potpurri/LiPo_Charger_TP4056_BuckBoost_TPS63020/imgs/3d-back-v1.1.png

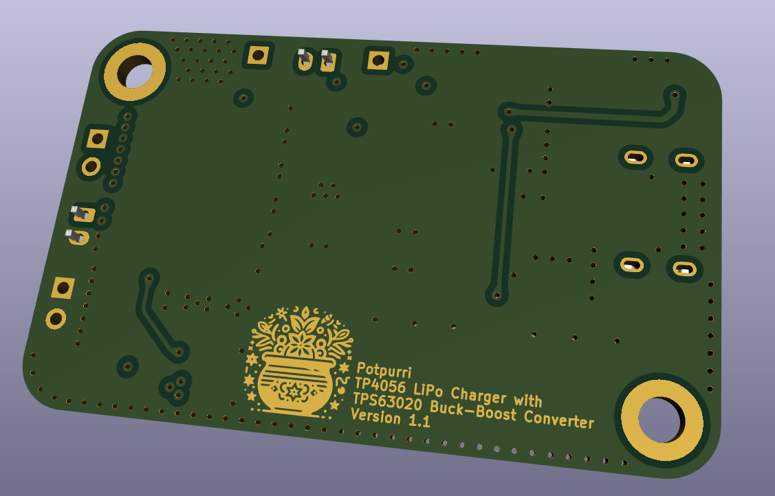
imgs/3d-back-v1.1.png
