potpurri/LiPo_Charger_TP4056_BuckBoost_TPS63020/imgs/3d-front-empty.png

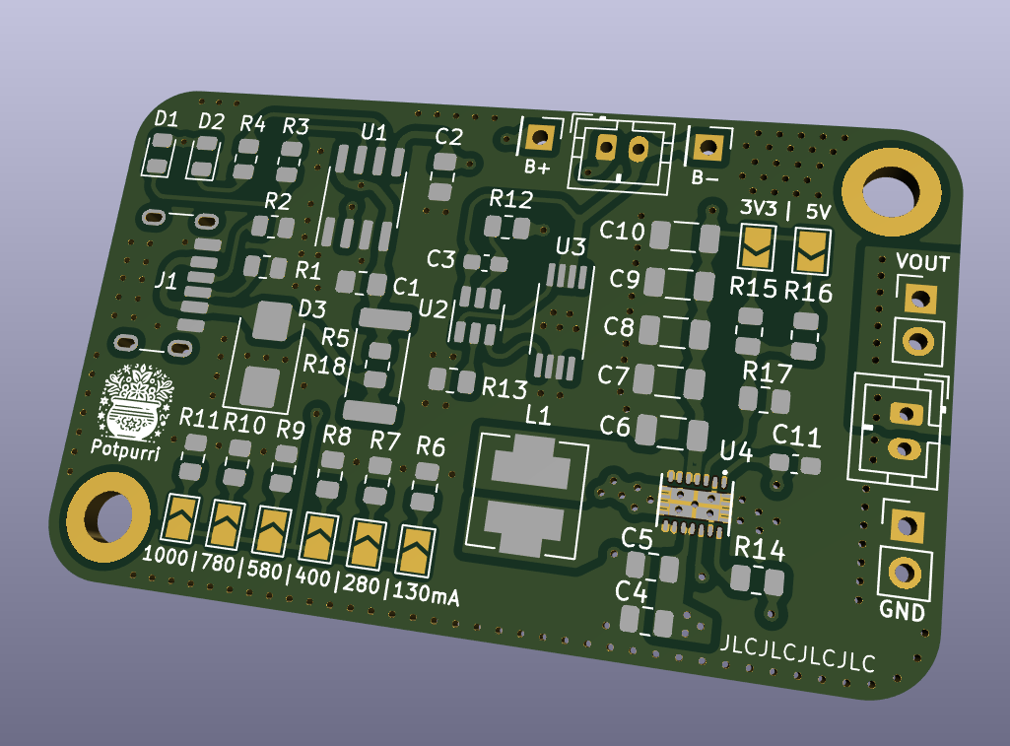
imgs/3d-front-empty.png
