potpurri/LiPo_Charger_TP4056_BuckBoost_TPS63020/imgs/pcb-back_v1.1.png

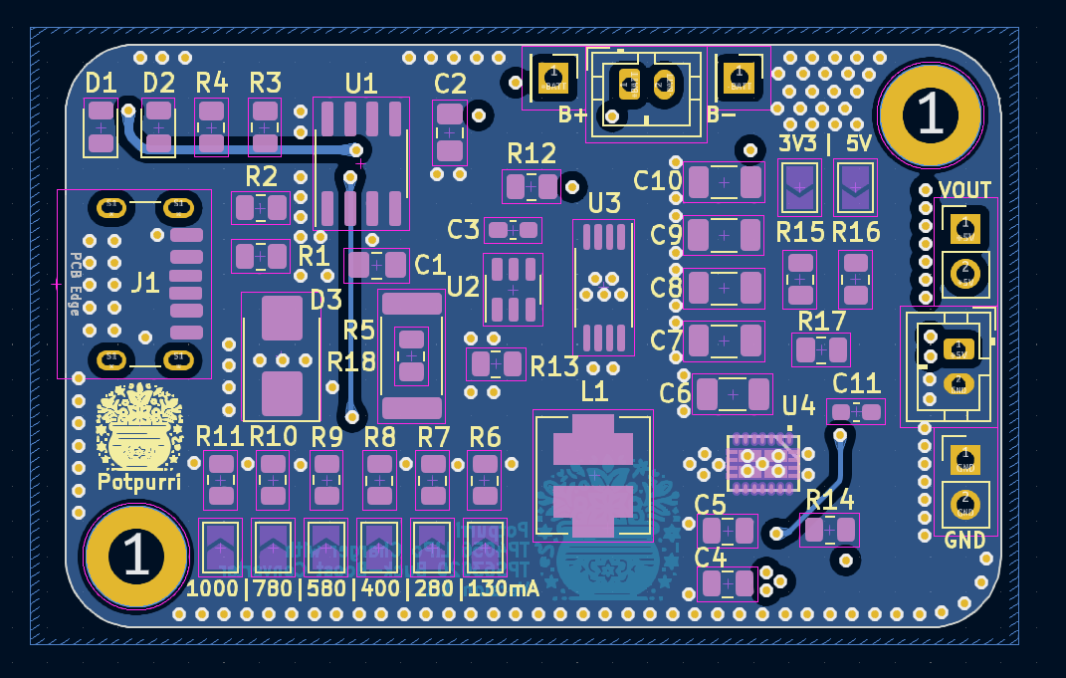
imgs/pcb-back_v1.1.png
