potpurri/LiPo_Charger_TP4056_BuckBoost_TPS63020/imgs/pcb-pwr_v1.1.png

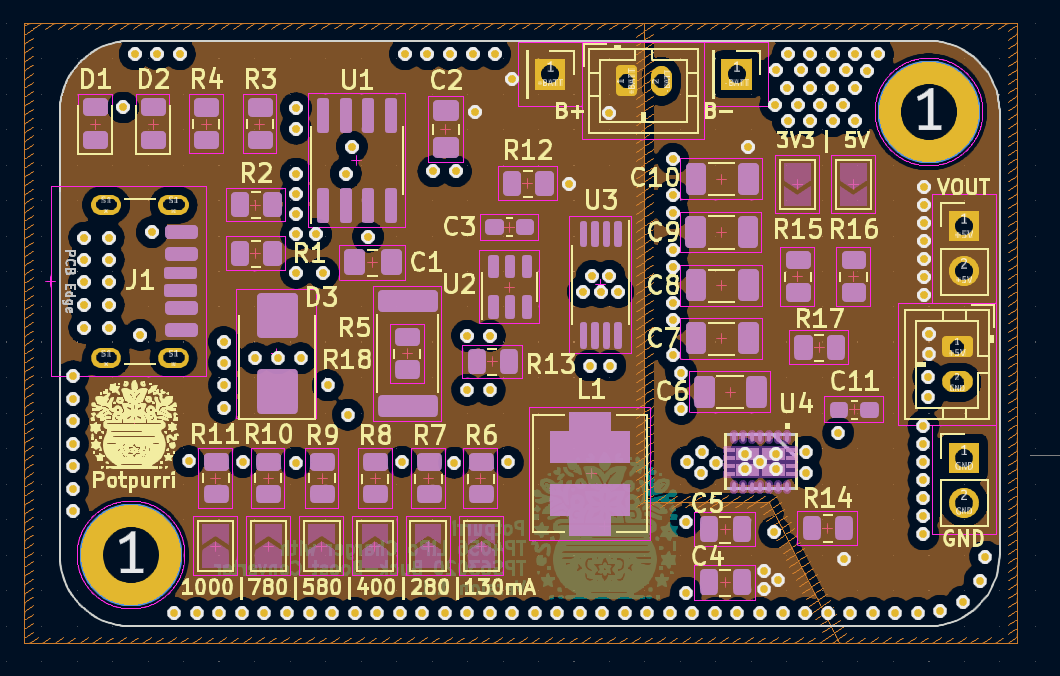
imgs/pcb-pwr_v1.1.png
