potpurri/LiPo_Charger_TP4056_BuckBoost_TPS63020/imgs/pccb.png

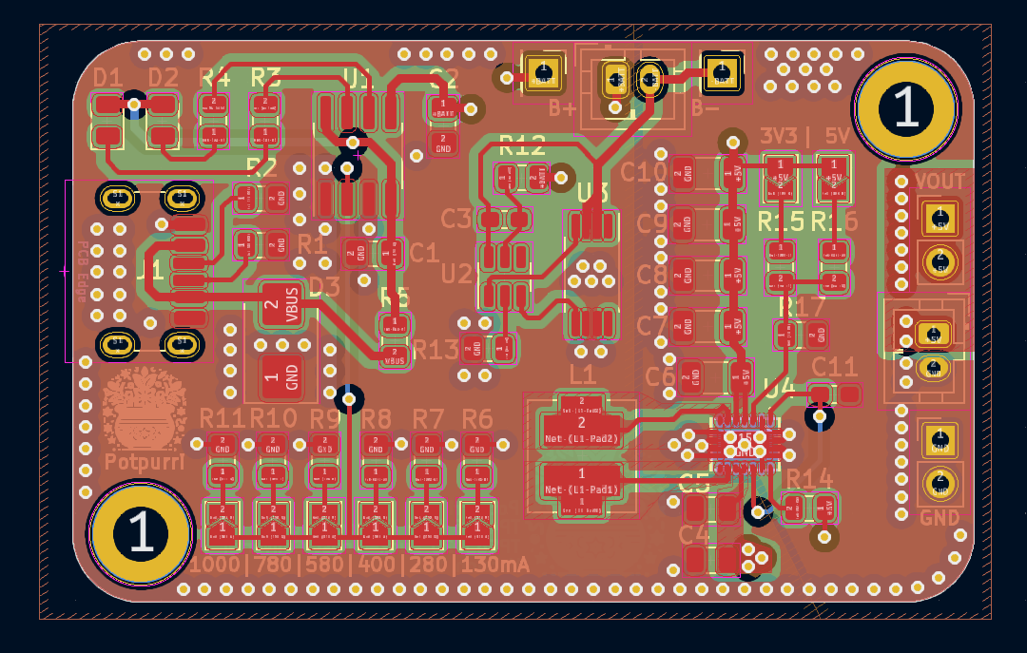
imgs/pccb.png
